ArnauldDev/kicad-project-power-switching-system/MECA/Add_LED_3mm_Red_18mm_Leads.png

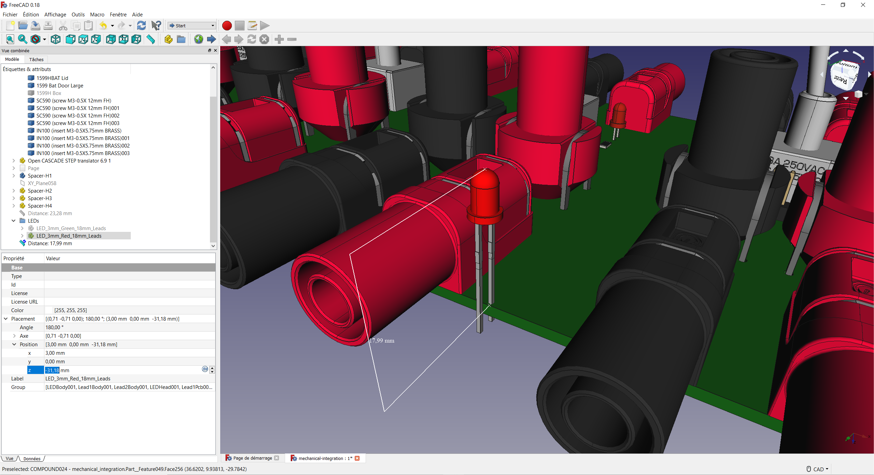
MECA/Add_LED_3mm_Red_18mm_Leads.png
